nsobczak/e-Holographer/Images/Capture_ConstellationConsole_1ereAppli.PNG

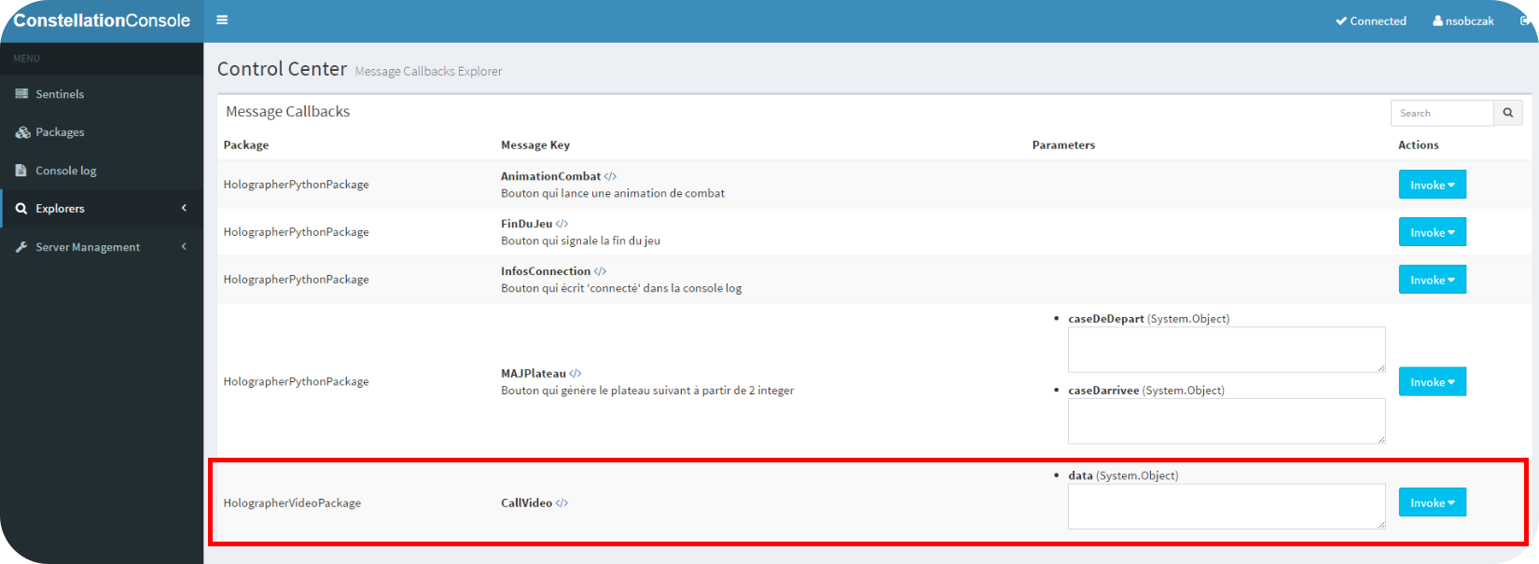
Images/Capture_ConstellationConsole_1ereAppli.PNG
