nsobczak/e-Holographer/Images/ChessGame/Capture_ConstellationConsole_SO.png

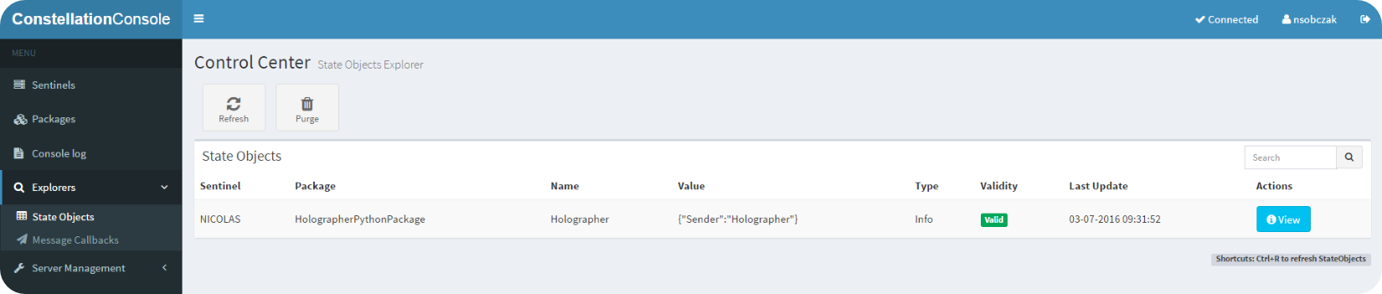
Images/ChessGame/Capture_ConstellationConsole_SO.png
