nsobczak/e-Holographer/Images/ChessGame/CaptureAppliWeb.PNG

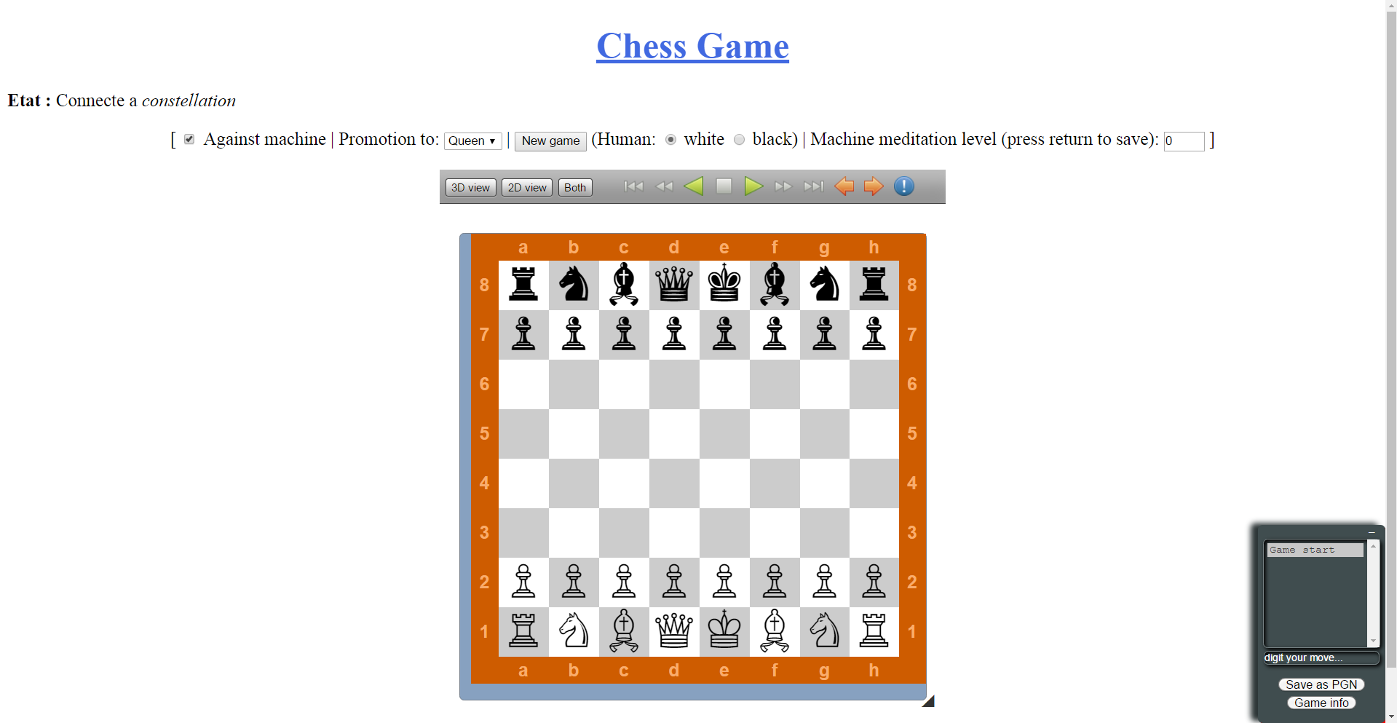
Images/ChessGame/CaptureAppliWeb.PNG
