nsobczak/e-Holographer/Images/ChessGame/Console log - connexion.PNG

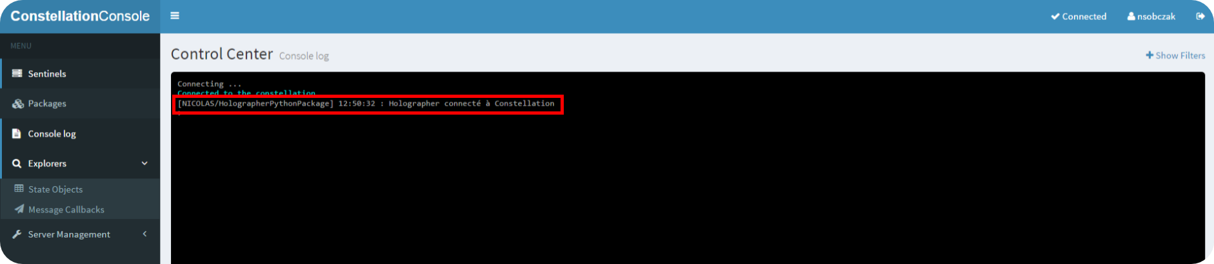
Images/ChessGame/Console log - connexion.PNG
