nsobczak/e-Holographer/Images/ChessGame/Console log - game over.PNG

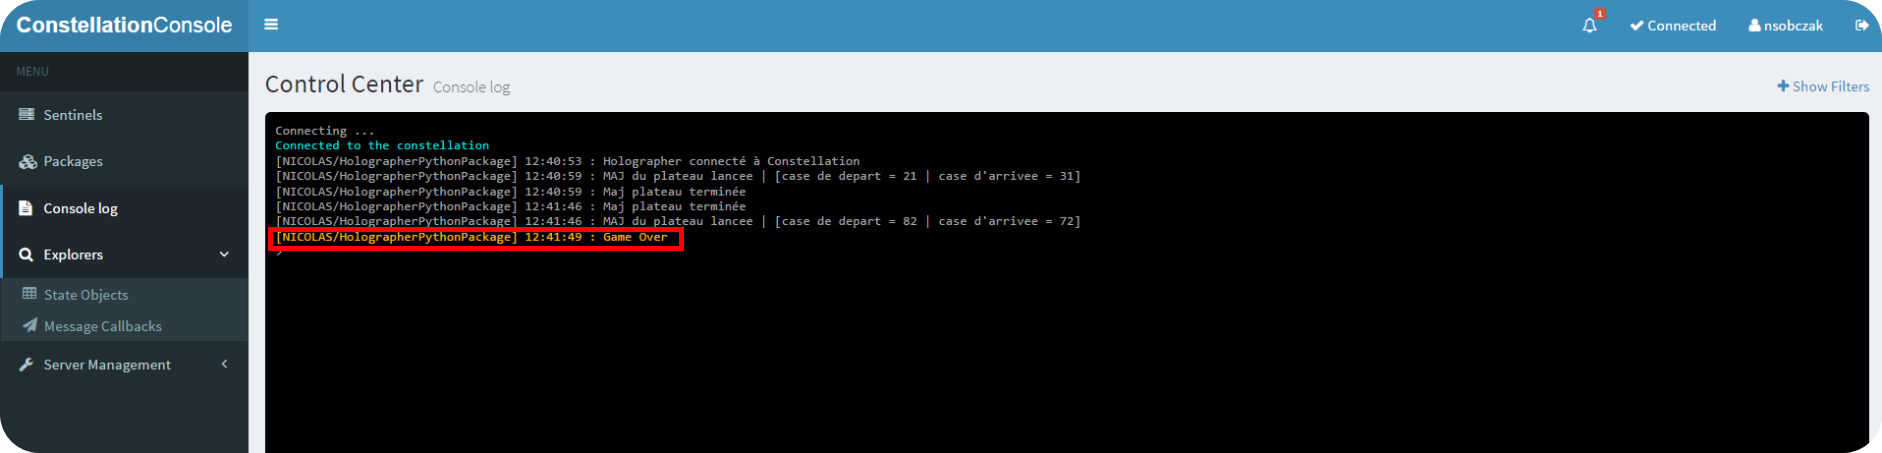
Images/ChessGame/Console log - game over.PNG
