nsobczak/e-Holographer/Images/ChessGame/Démo jeu d'échec holographique.PNG

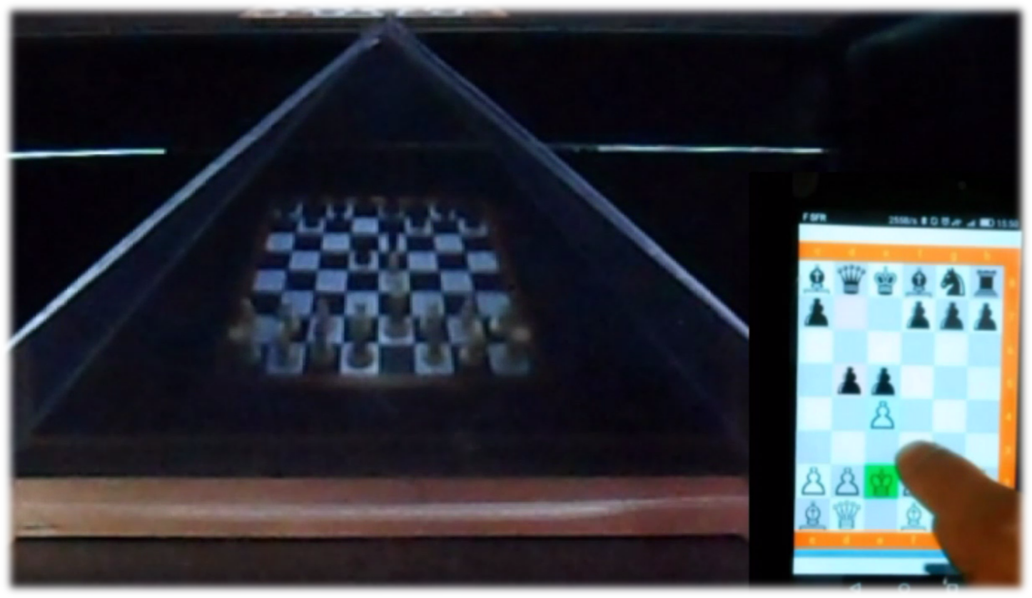
Images/ChessGame/Démo jeu d'échec holographique.PNG
