nsobczak/e-Holographer/Images/ChessGame/PlateauInitialFront.png

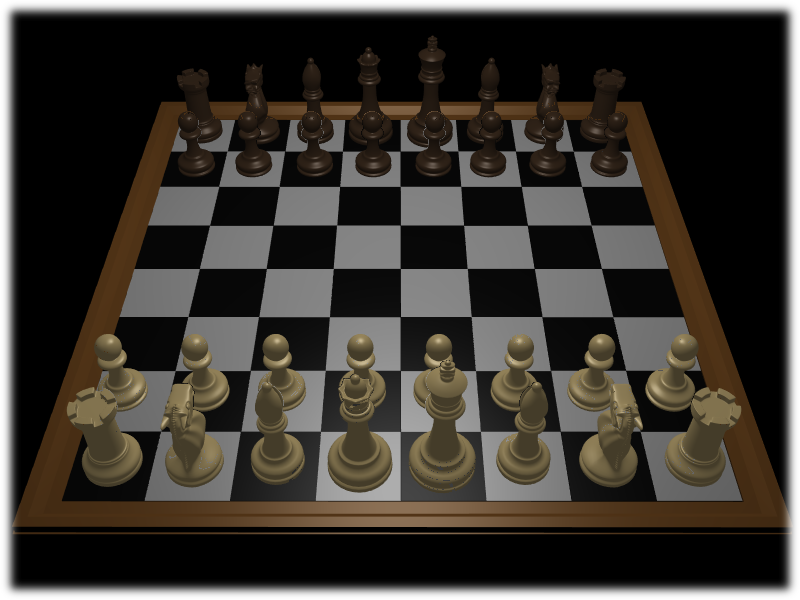
Images/ChessGame/PlateauInitialFront.png
