nsobczak/e-Holographer/Images/La méduse hologramme.PNG

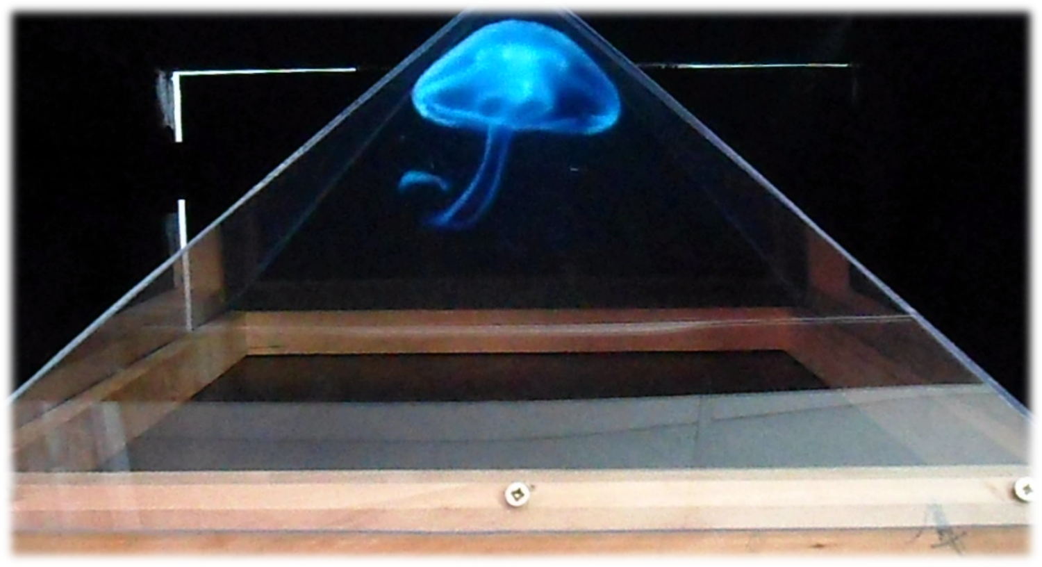
Images/La méduse hologramme.PNG
