nsobczak/e-Holographer/Images/Pyramide.png

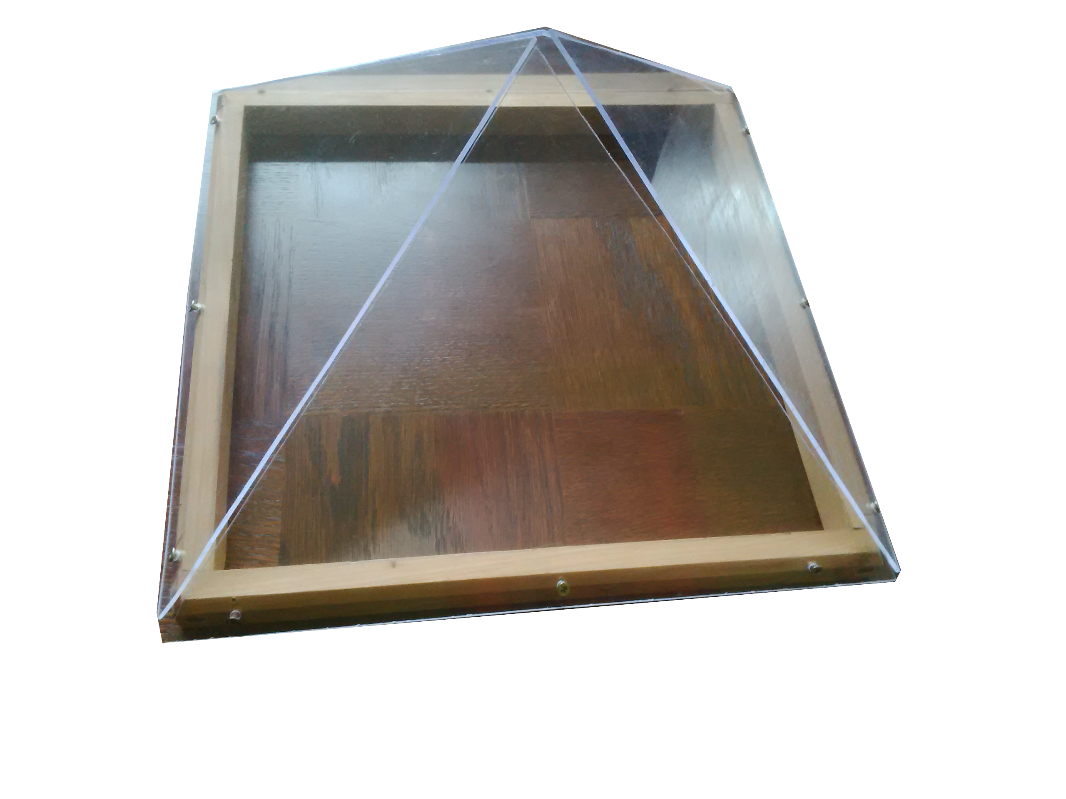
Images/Pyramide.png
