nsobczak/e-Holographer/Images/Schéma appli,constellation,package.png

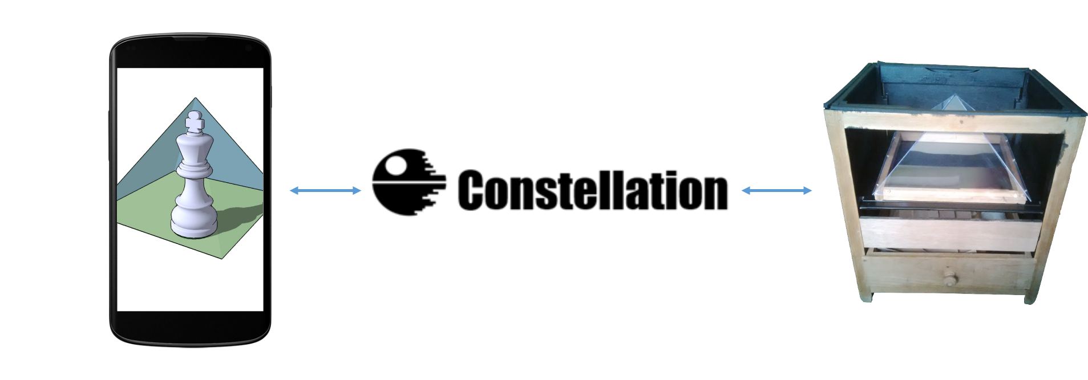
Images/Schéma appli,constellation,package.png
