nsobczak/e-Holographer/Images/Schéma e-Holographer.png

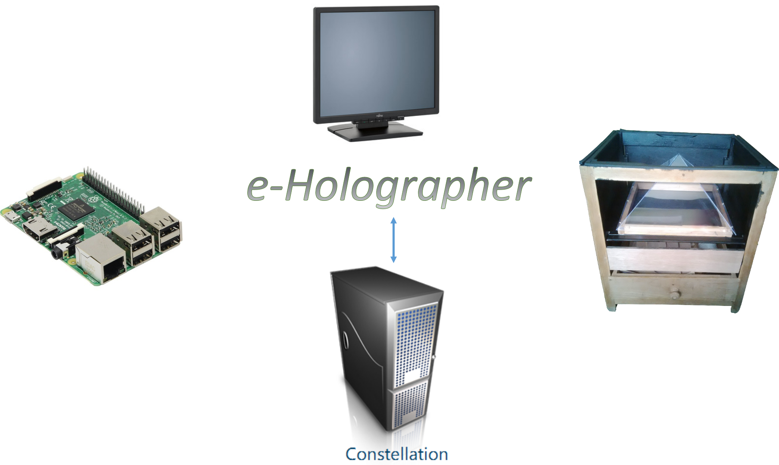
Images/Schéma e-Holographer.png
